skyapem01/Mudskipper_Robot/Mudskipper_Solid2022/Mudskipper_Solid2022/Stud_41m - Copy.SLDPRT

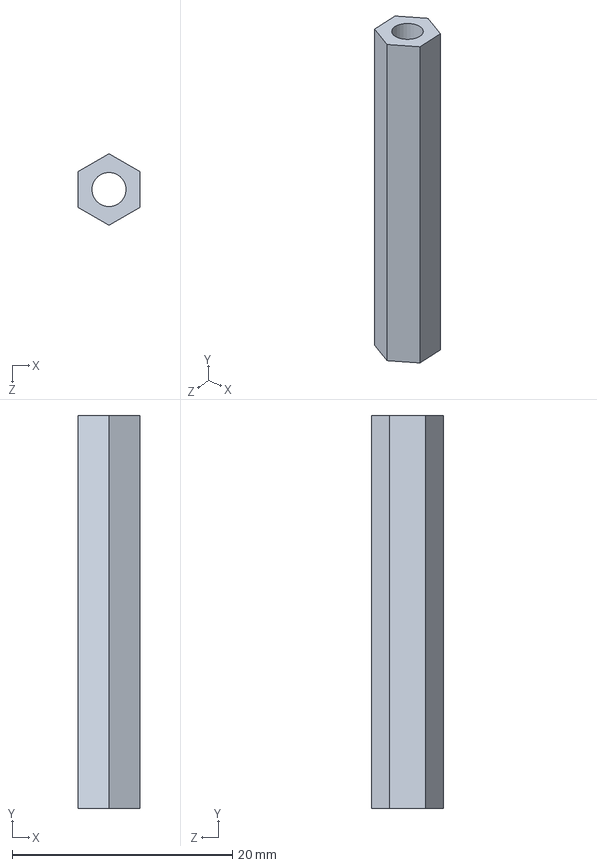
[picture p36: CAD file, 2023-05-24, an earlier design]
Mudskipper_Solid2022/Mudskipper_Solid2022/Stud_41m - Copy.SLDPRT
5.63 x 35.7 x 6.50 mm
